newHeiko/WiFi-JMRI-Clock/documentation/images/DSC1138.jpg

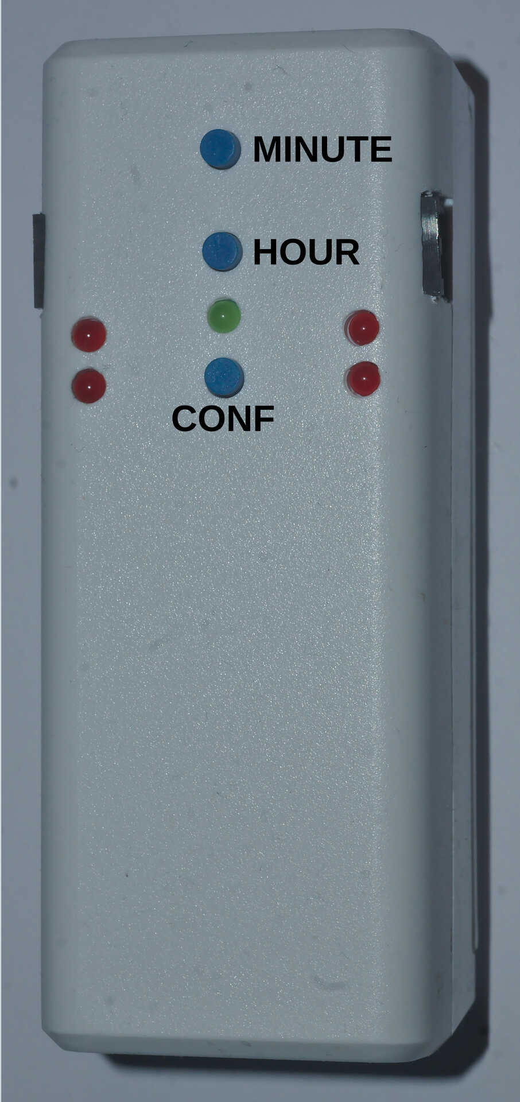
documentation/images/DSC1138.jpg
