newHeiko/WiFi-JMRI-Clock/documentation/images/DSC1139.jpg

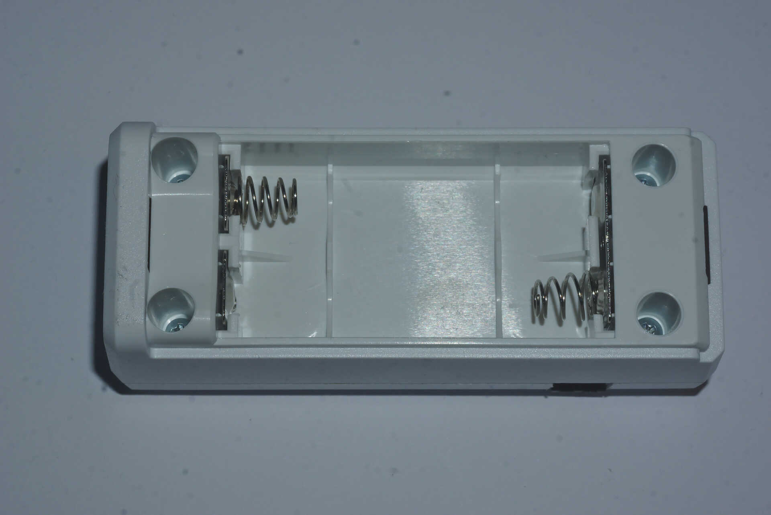
documentation/images/DSC1139.jpg
