newHeiko/WiFi-JMRI-Clock/documentation/images/DSC1141.jpg

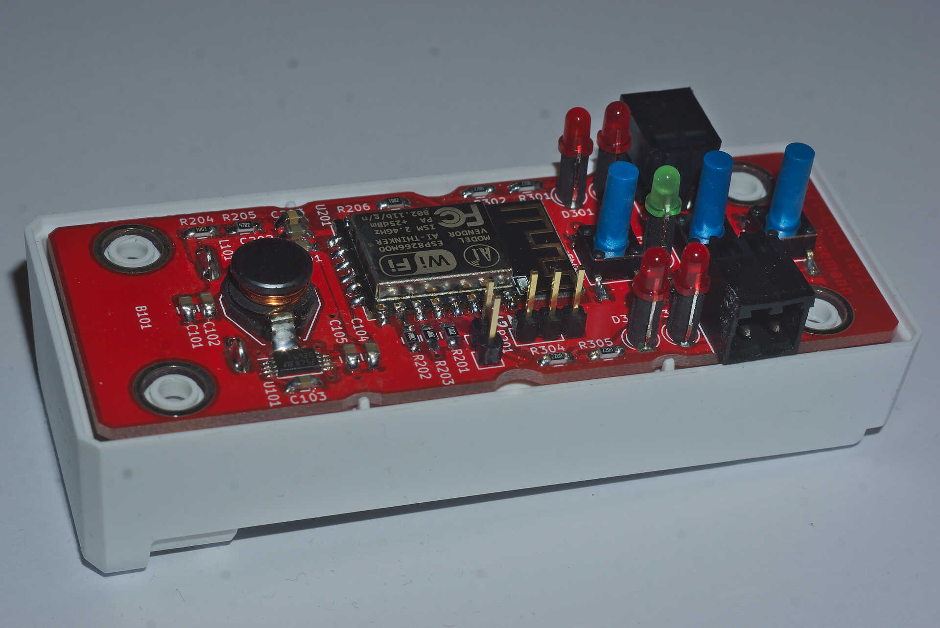
documentation/images/DSC1141.jpg
